dwaq/particle-squared-hardware/Eagle-Renders/pm25.brd.png

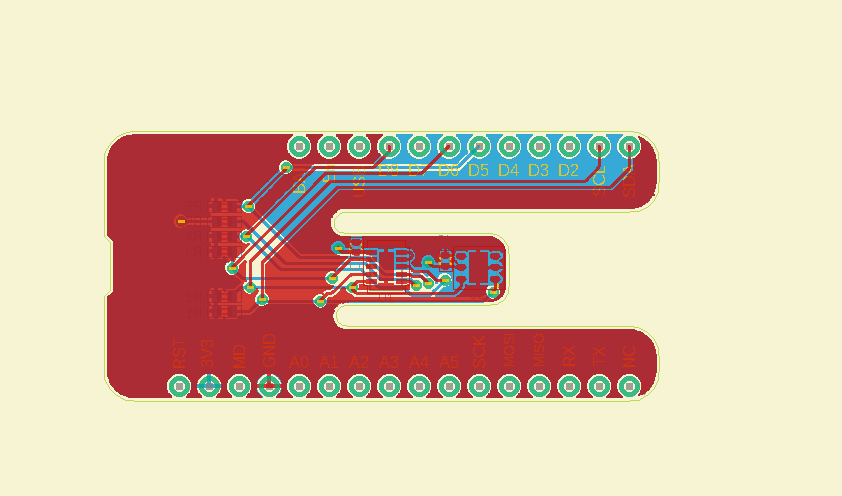
Eagle-Renders/pm25.brd.png
